WildernessLabs/Netduino_Hardware/N1_Plus/N1Plus_31Aug2010_RevB.pdf

## Power Connector +7.5V to +12V DC Input (9V Preferred)

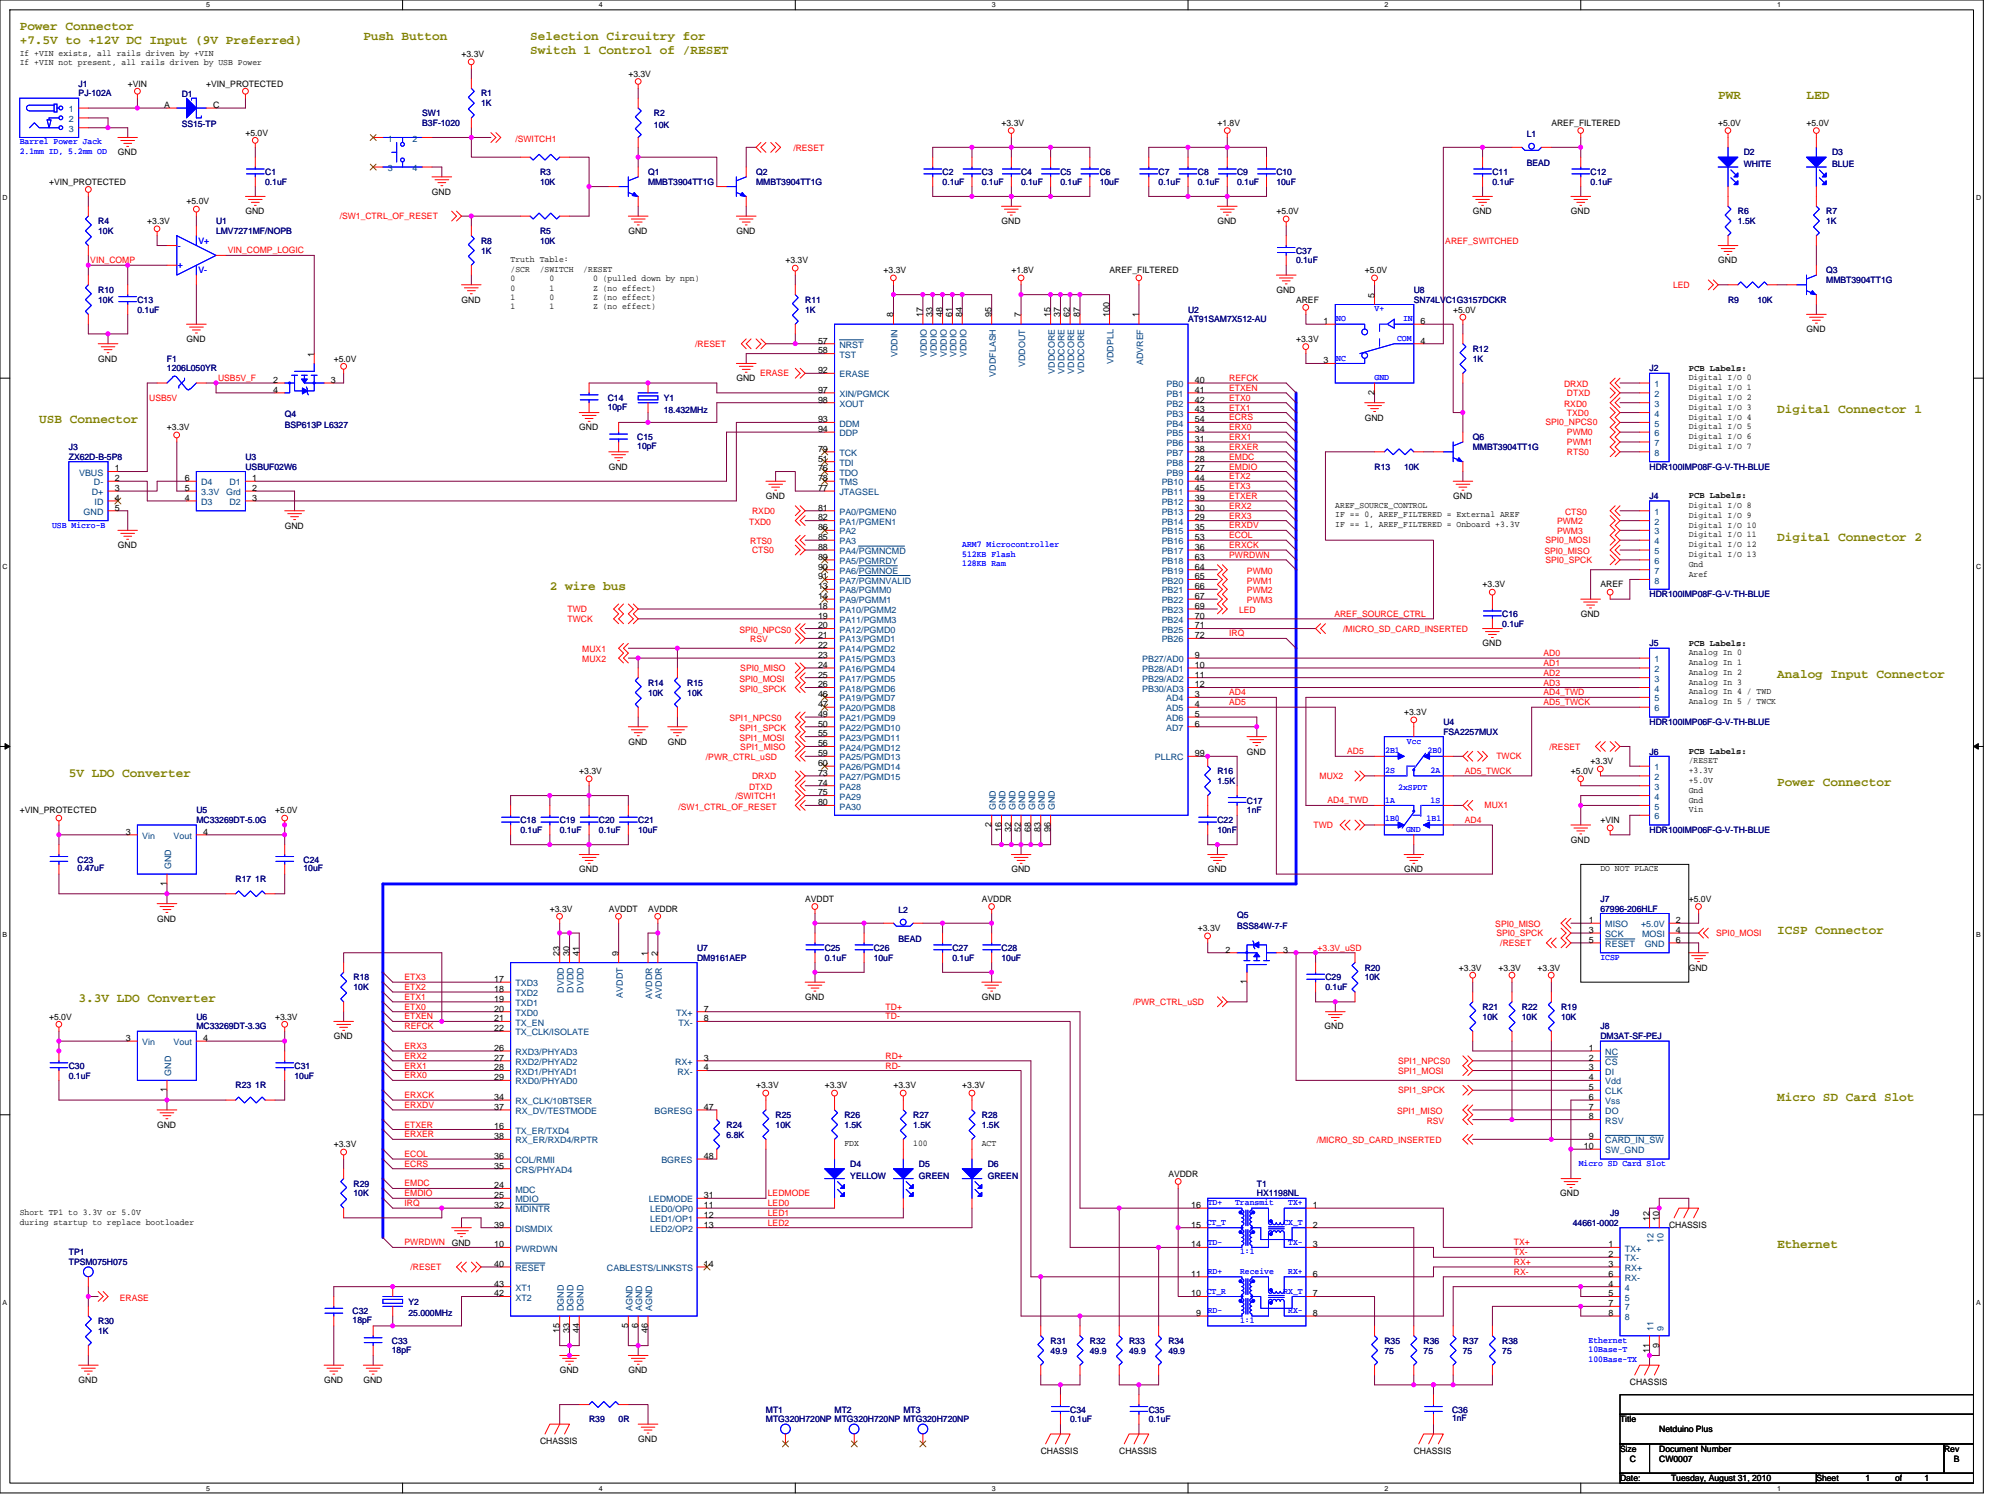
[picture p7: page 1]

Selection Circuitry for
Switch 1 Control of /RESET

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

Micro SD Card Slot

Short TP1 to 3.3V or 5.0V
during startup to replace bootloader
