WildernessLabs/Netduino_Hardware/N2/N2_20Dec16.pdf

## Power Connector

+7V to +9V DC Input | 5V LDO Converter

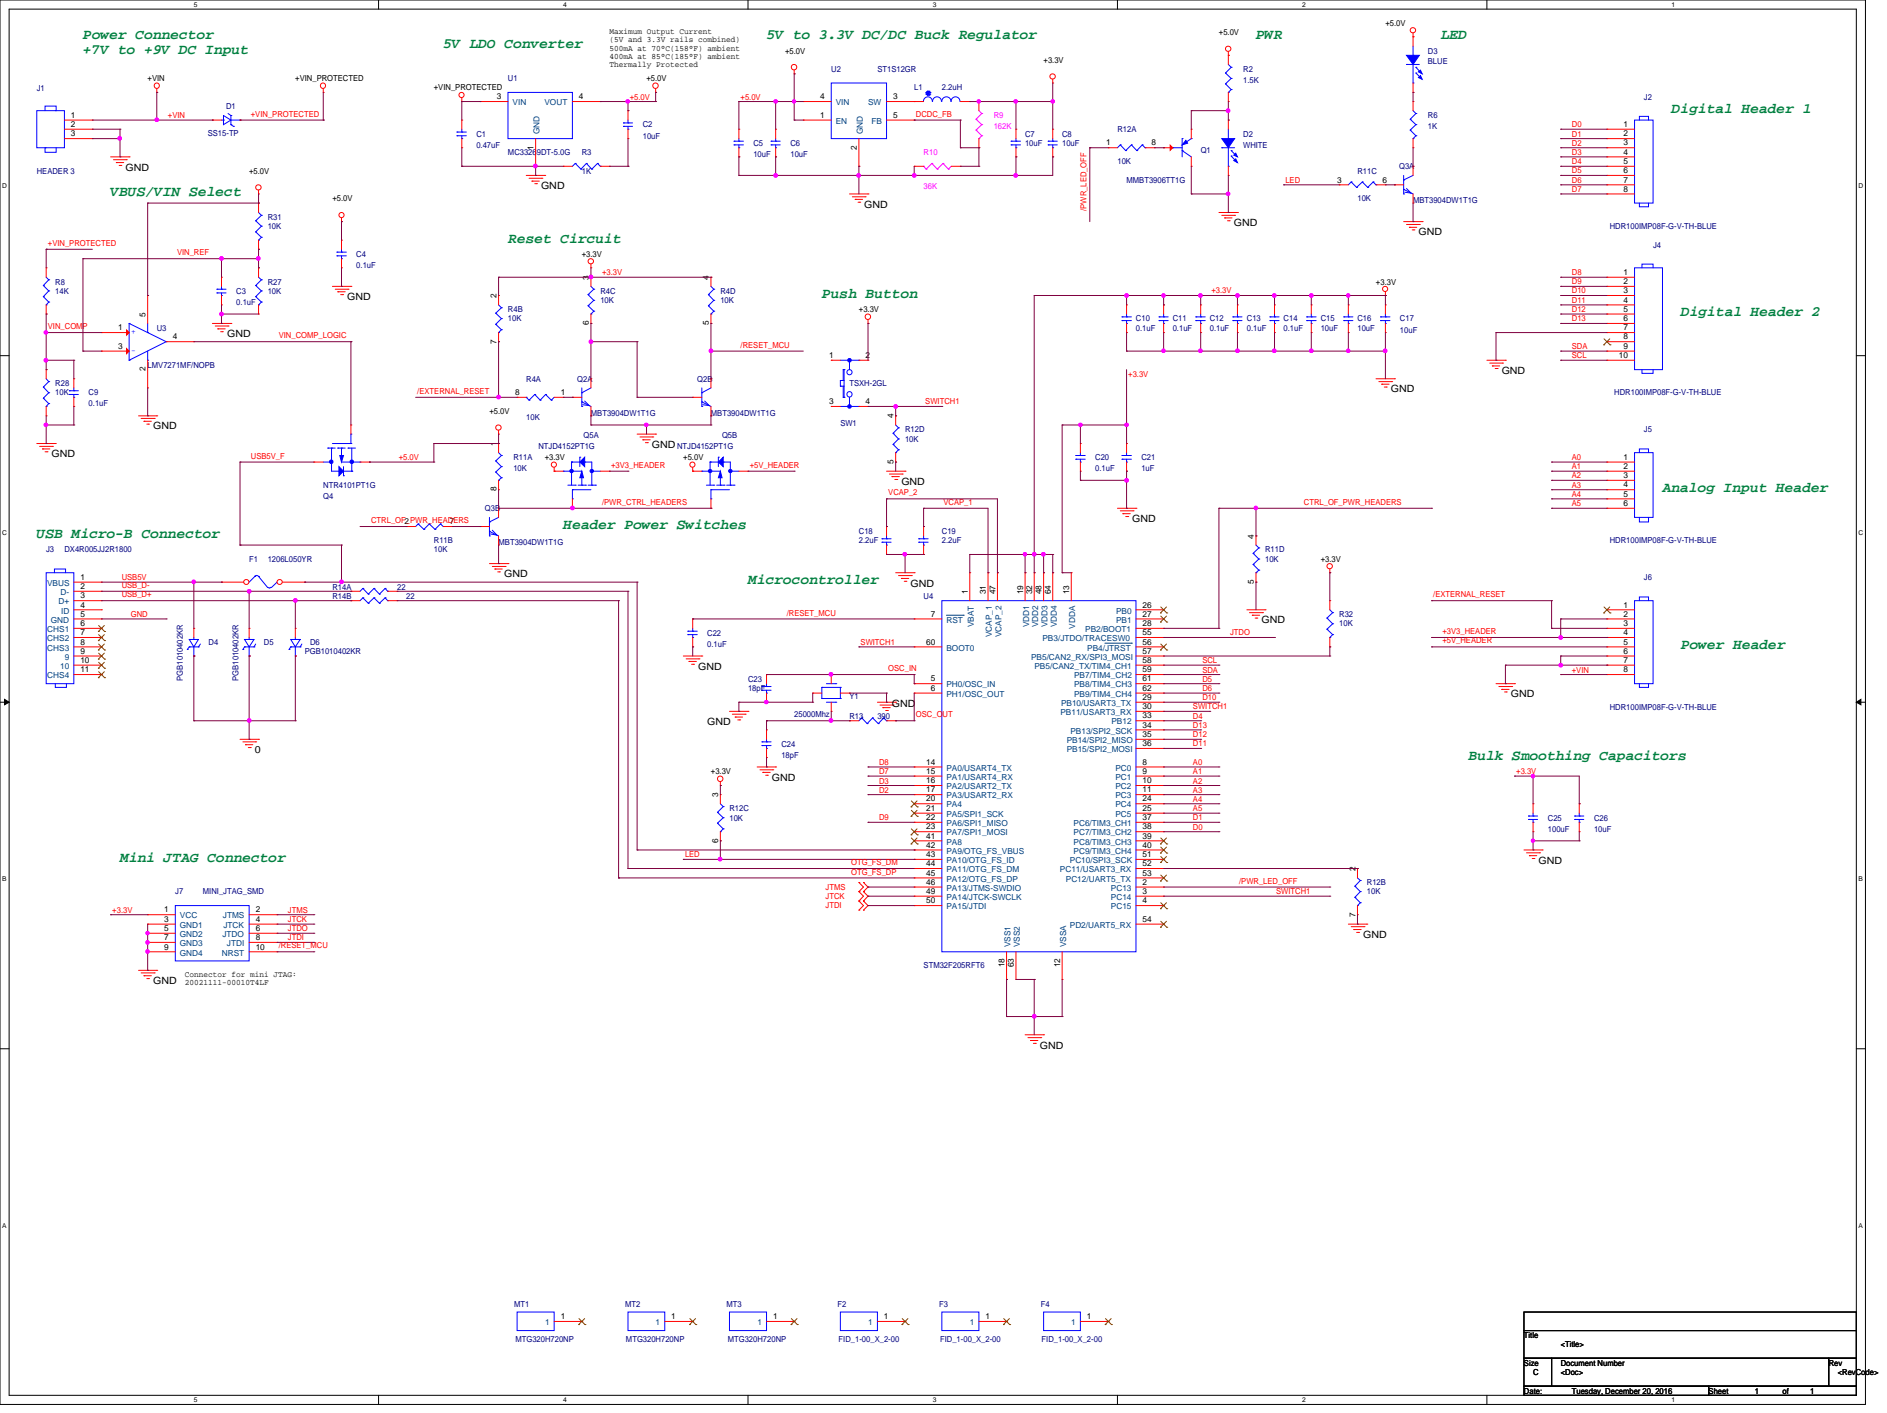
[picture p8: page 1]

5V to 3.3V DC/DC Buck Regulator

41 PA9/OTG_FS_VBUS 42 PA10/OTG_FS_ID 43 PA11/OTG_FS_DM 44 PA12/OTG_FS_DP 45 PA13/JTMS-SWDIO 46 PA14/JTCK-SWCLK 49 PA15/JTDI 50

Connector for mini JTAG:
GND
