WildernessLabs/Netduino_Hardware/N2_Plus/N2_PLUS_20DEC16_0800.pdf

## Power Connector

+7V to +9V DC Input | 5V LDO Converter

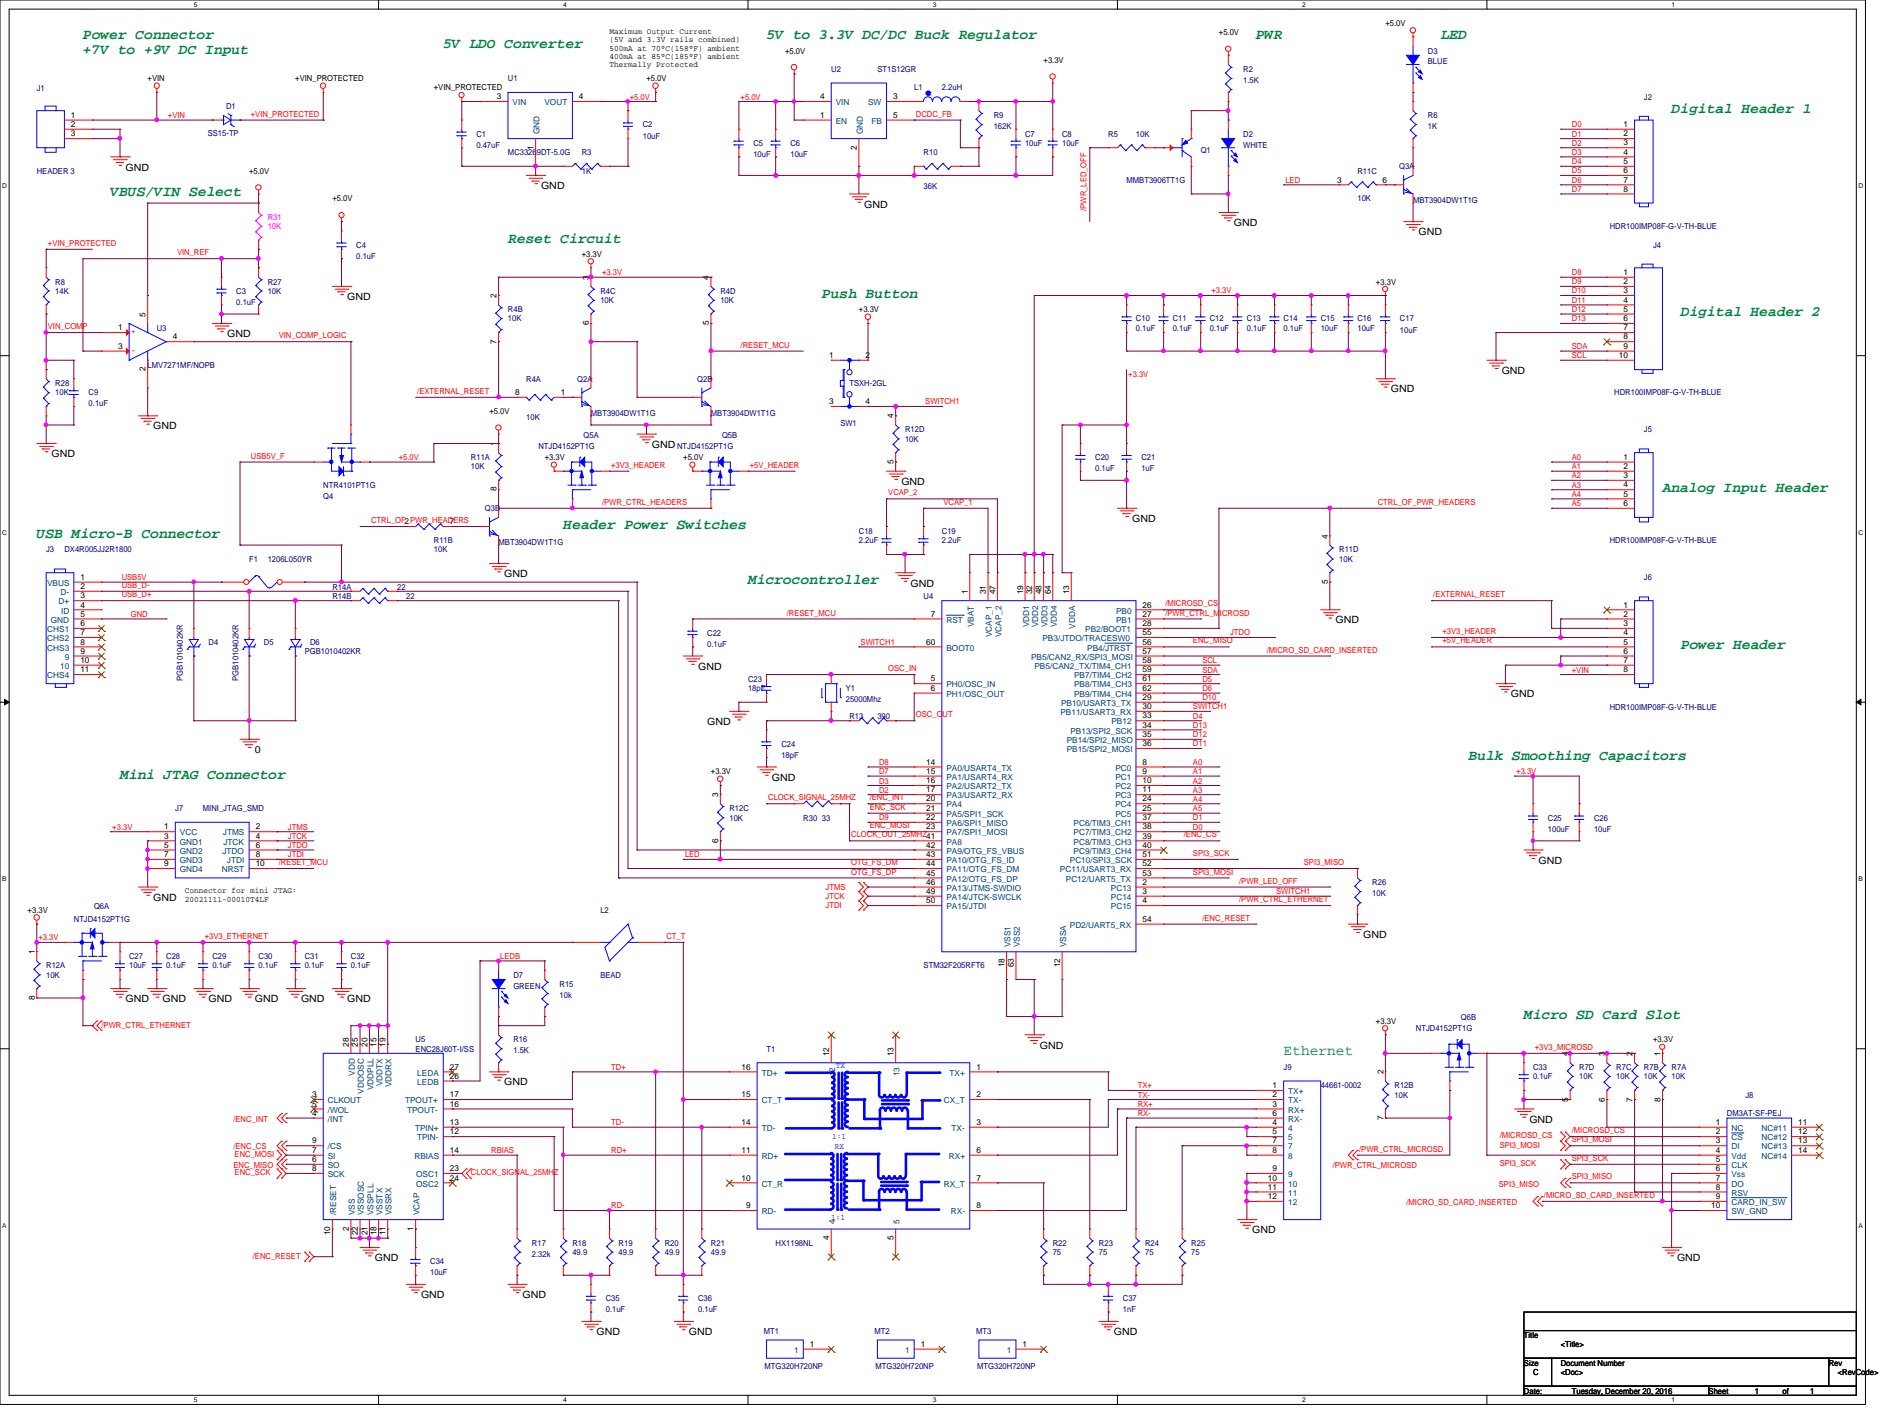
[picture p9: page 1]

5V to 3.3V DC/DC Buck Regulator

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

Connector for mini JTAG:
GND

Micro SD Card Slot

27 VDDRX ¹⁹ VDDTX ¹⁵ VDDPLL 20 VDDOSC ²⁵ VDD ²⁸

J8 DM3AT-SF-PEJ NC 1 CS 2 DI 3 Vdd

4 CLK 5 Vss 6 DO 7 RSV 8 CARD_IN_SW 9 SW_GND 10

2 VSSOSC 22 VSSPLL 21 VSSTX 18 VSSRX 11 VCAP
