WildernessLabs/Netduino_Hardware/N3/NETDUINO3_16DEC16.pdf

## Power Connector

+7V to +12V DC Input | 5V LDO Converter | 5V to 3.3V DC/DC Buck Regulator

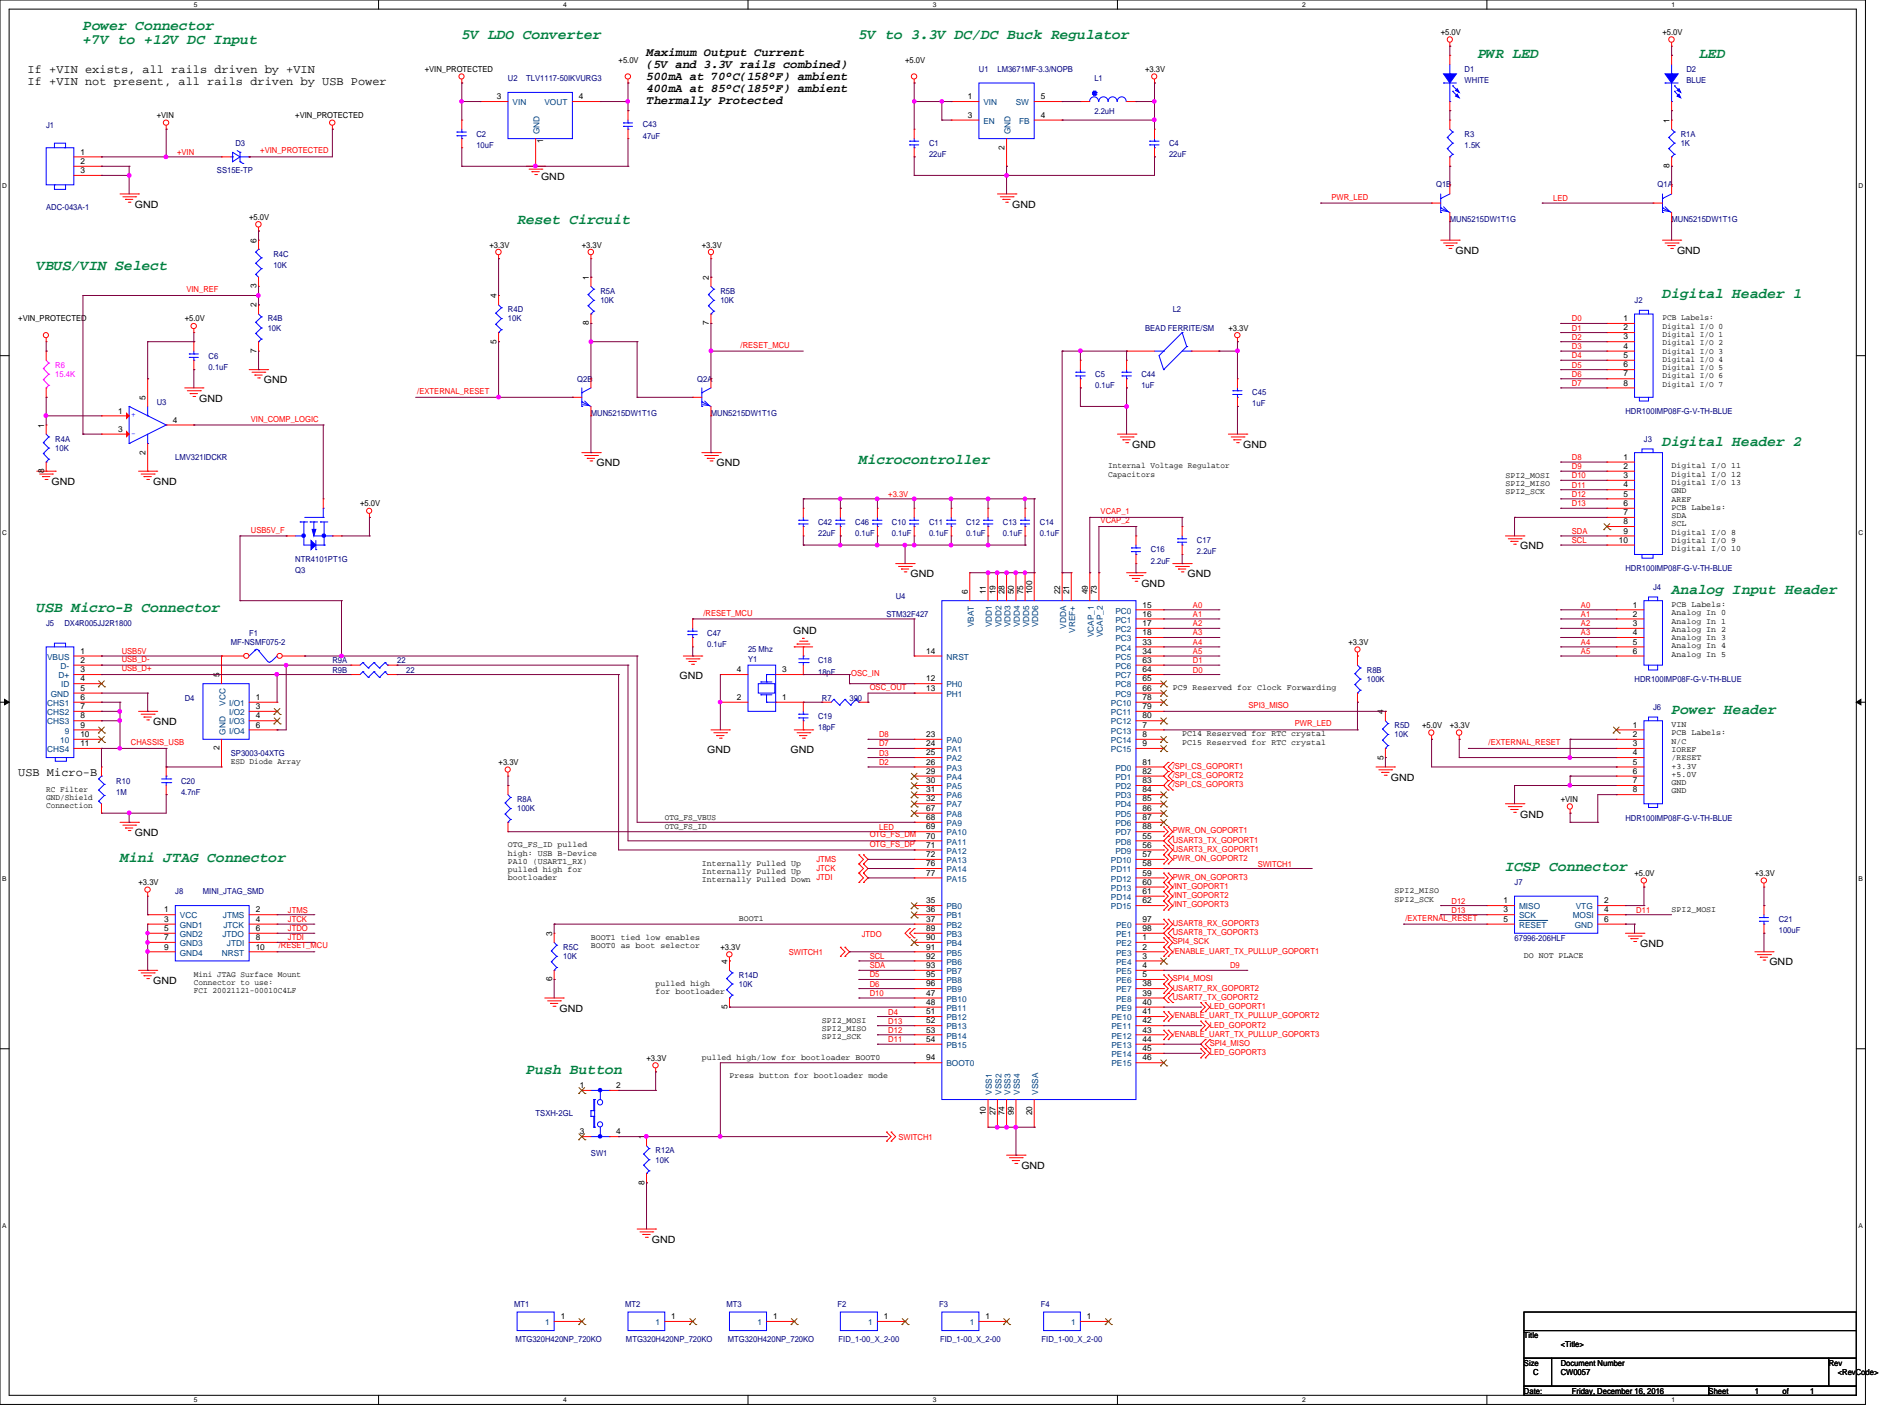
[picture p10: page 1]

If +VIN exists, all rails driven by +VIN
If +VIN not present, all rails driven by USB Power

PC9 Reserved for Clock Forwarding

PC14 Reserved for RTC crystal
PC15 Reserved for RTC crystal

Mini JTAG Surface Mount
Connector to use:
FCI 20021121-00010C4LF

pulled high/low for bootloader BOOT0

Press button for bootloader mode

## GoPort Power Switches

## GoPort1

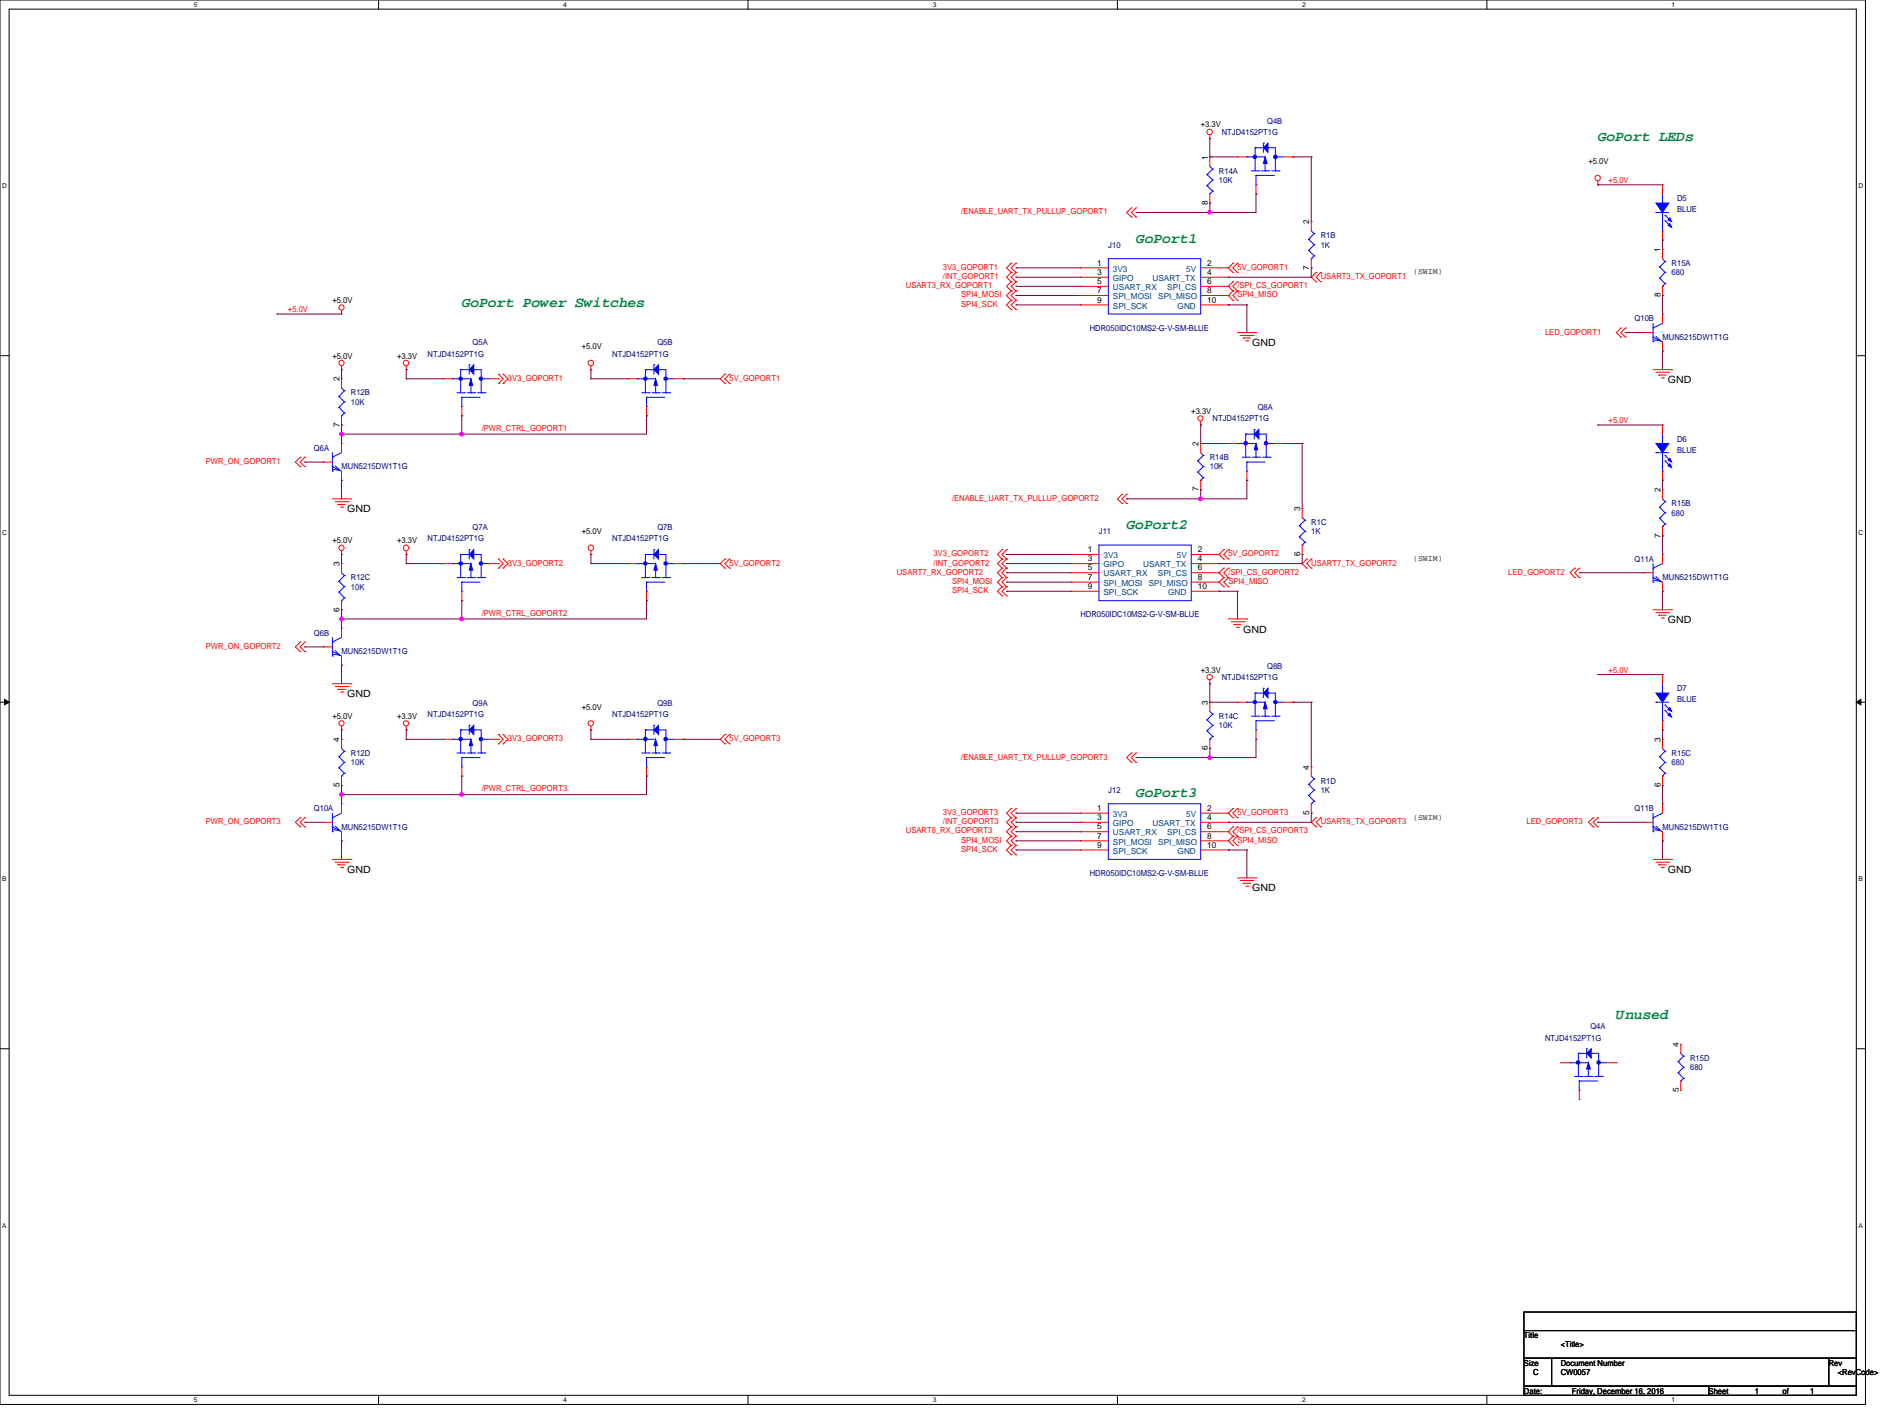
[picture p11: page 2]
