WildernessLabs/Netduino_Hardware/N3_Ethernet/N3_ETHENET_17DEC16_1415.pdf

## Power Connector

+7V to +12V DC Input | 5V LDO Converter | 5V to 3.3V DC/DC Buck Regulator

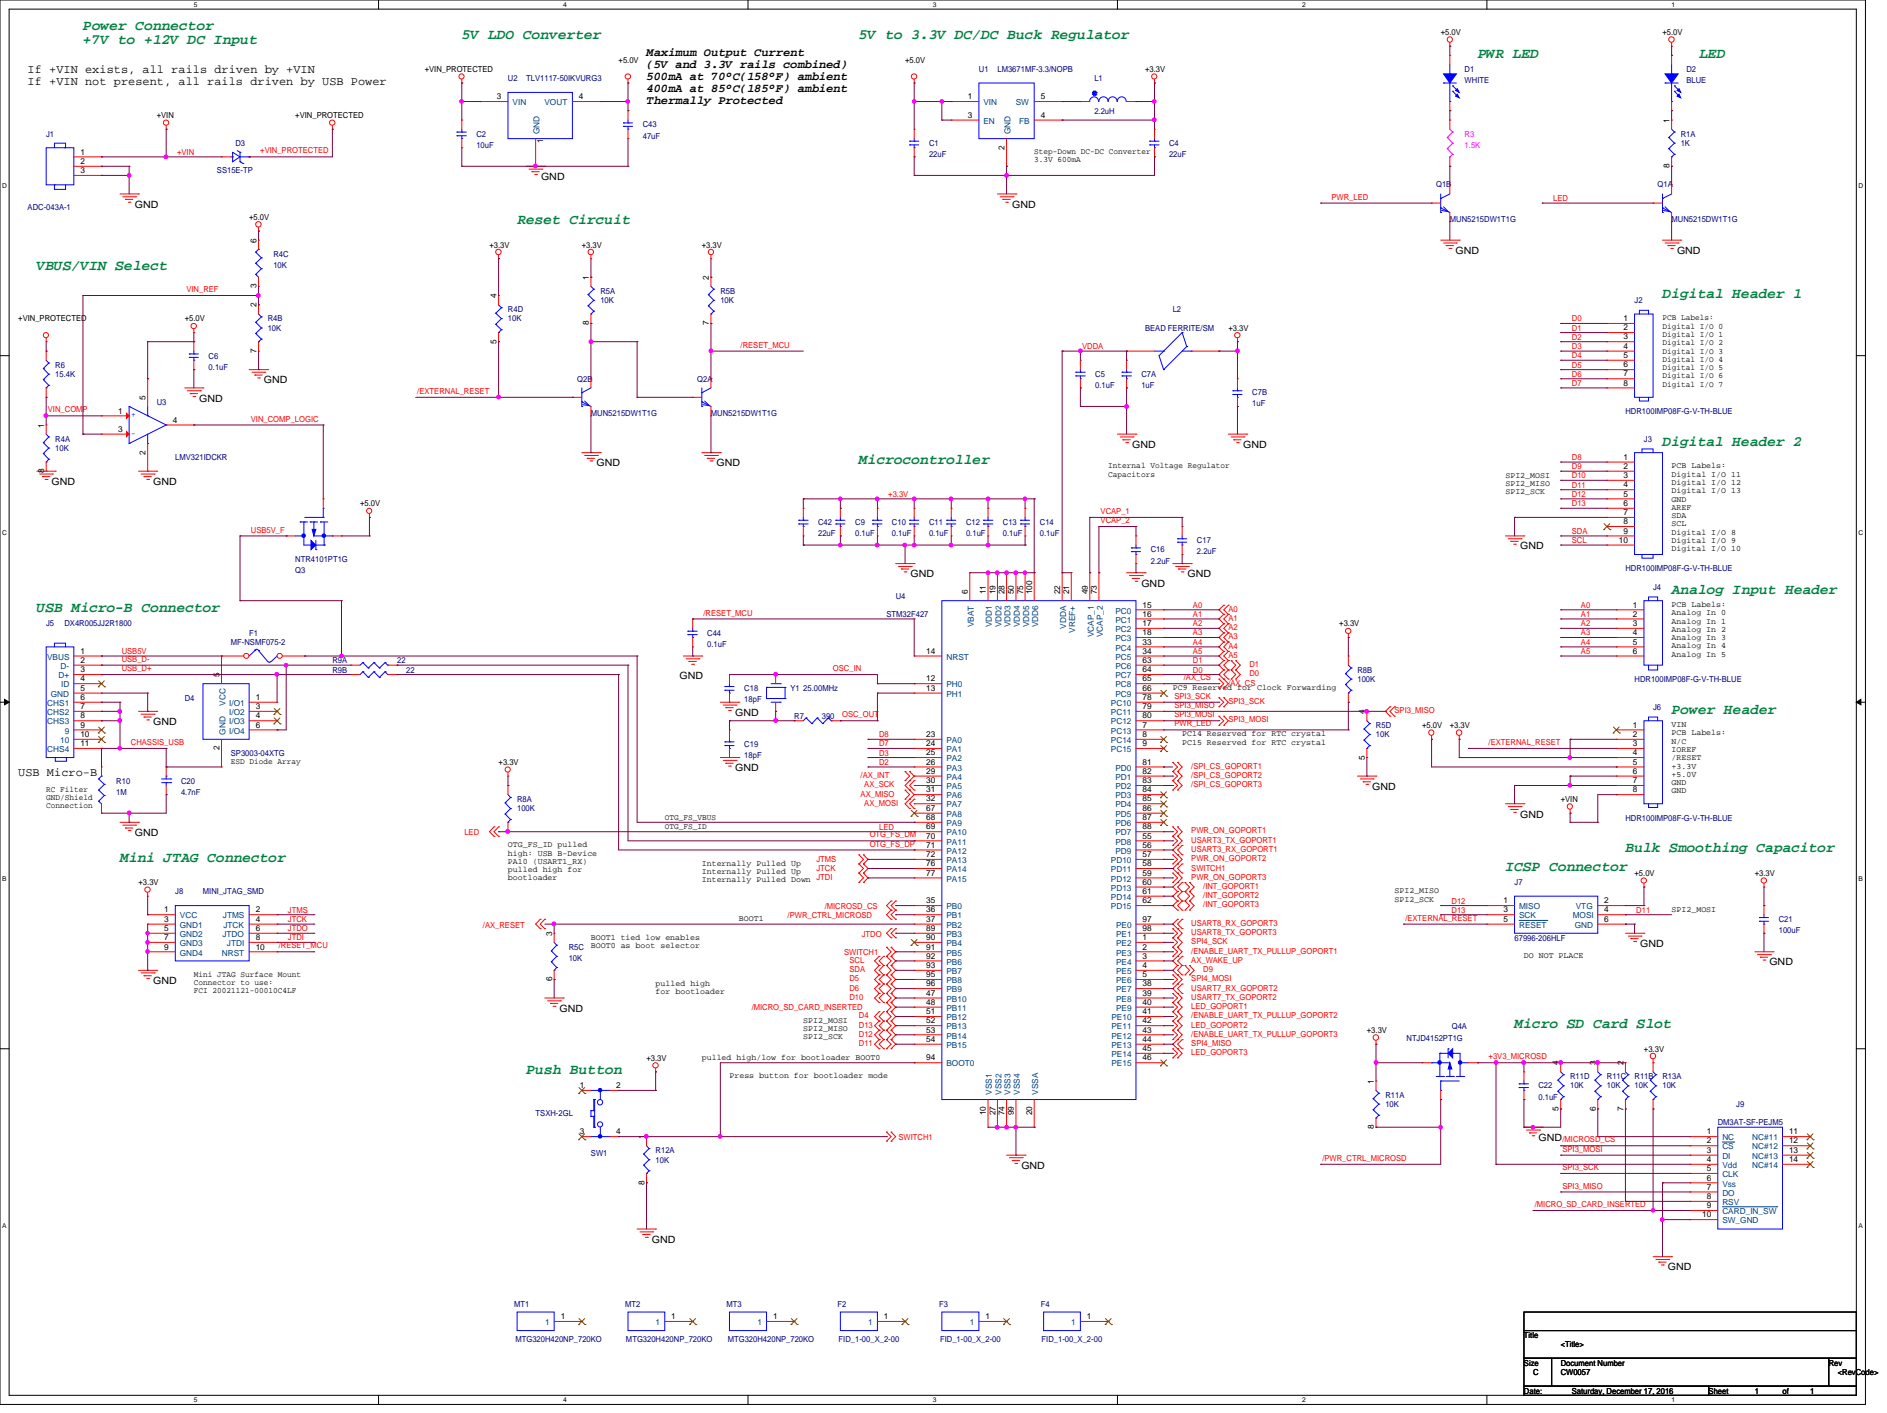
[picture p12: page 1]

If +VIN exists, all rails driven by +VIN
If +VIN not present, all rails driven by USB Power

Step-Down DC-DC Converter

PC14 Reserved for RTC crystal
PC15 Reserved for RTC crystal

Mini JTAG Surface Mount
Connector to use:
FCI 20021121-00010C4LF

Micro SD Card Slot

pulled high/low for bootloader BOOT0

Press button for bootloader mode

J9 DM3AT-SF-PEJM5 NC 1 CS 2 DI 3 Vdd

4 CLK 5 Vss 6 DO 7 RSV 8 CARD_IN_SW 9 SW_GND 10

## GoPort Power Switches

## GoPort1

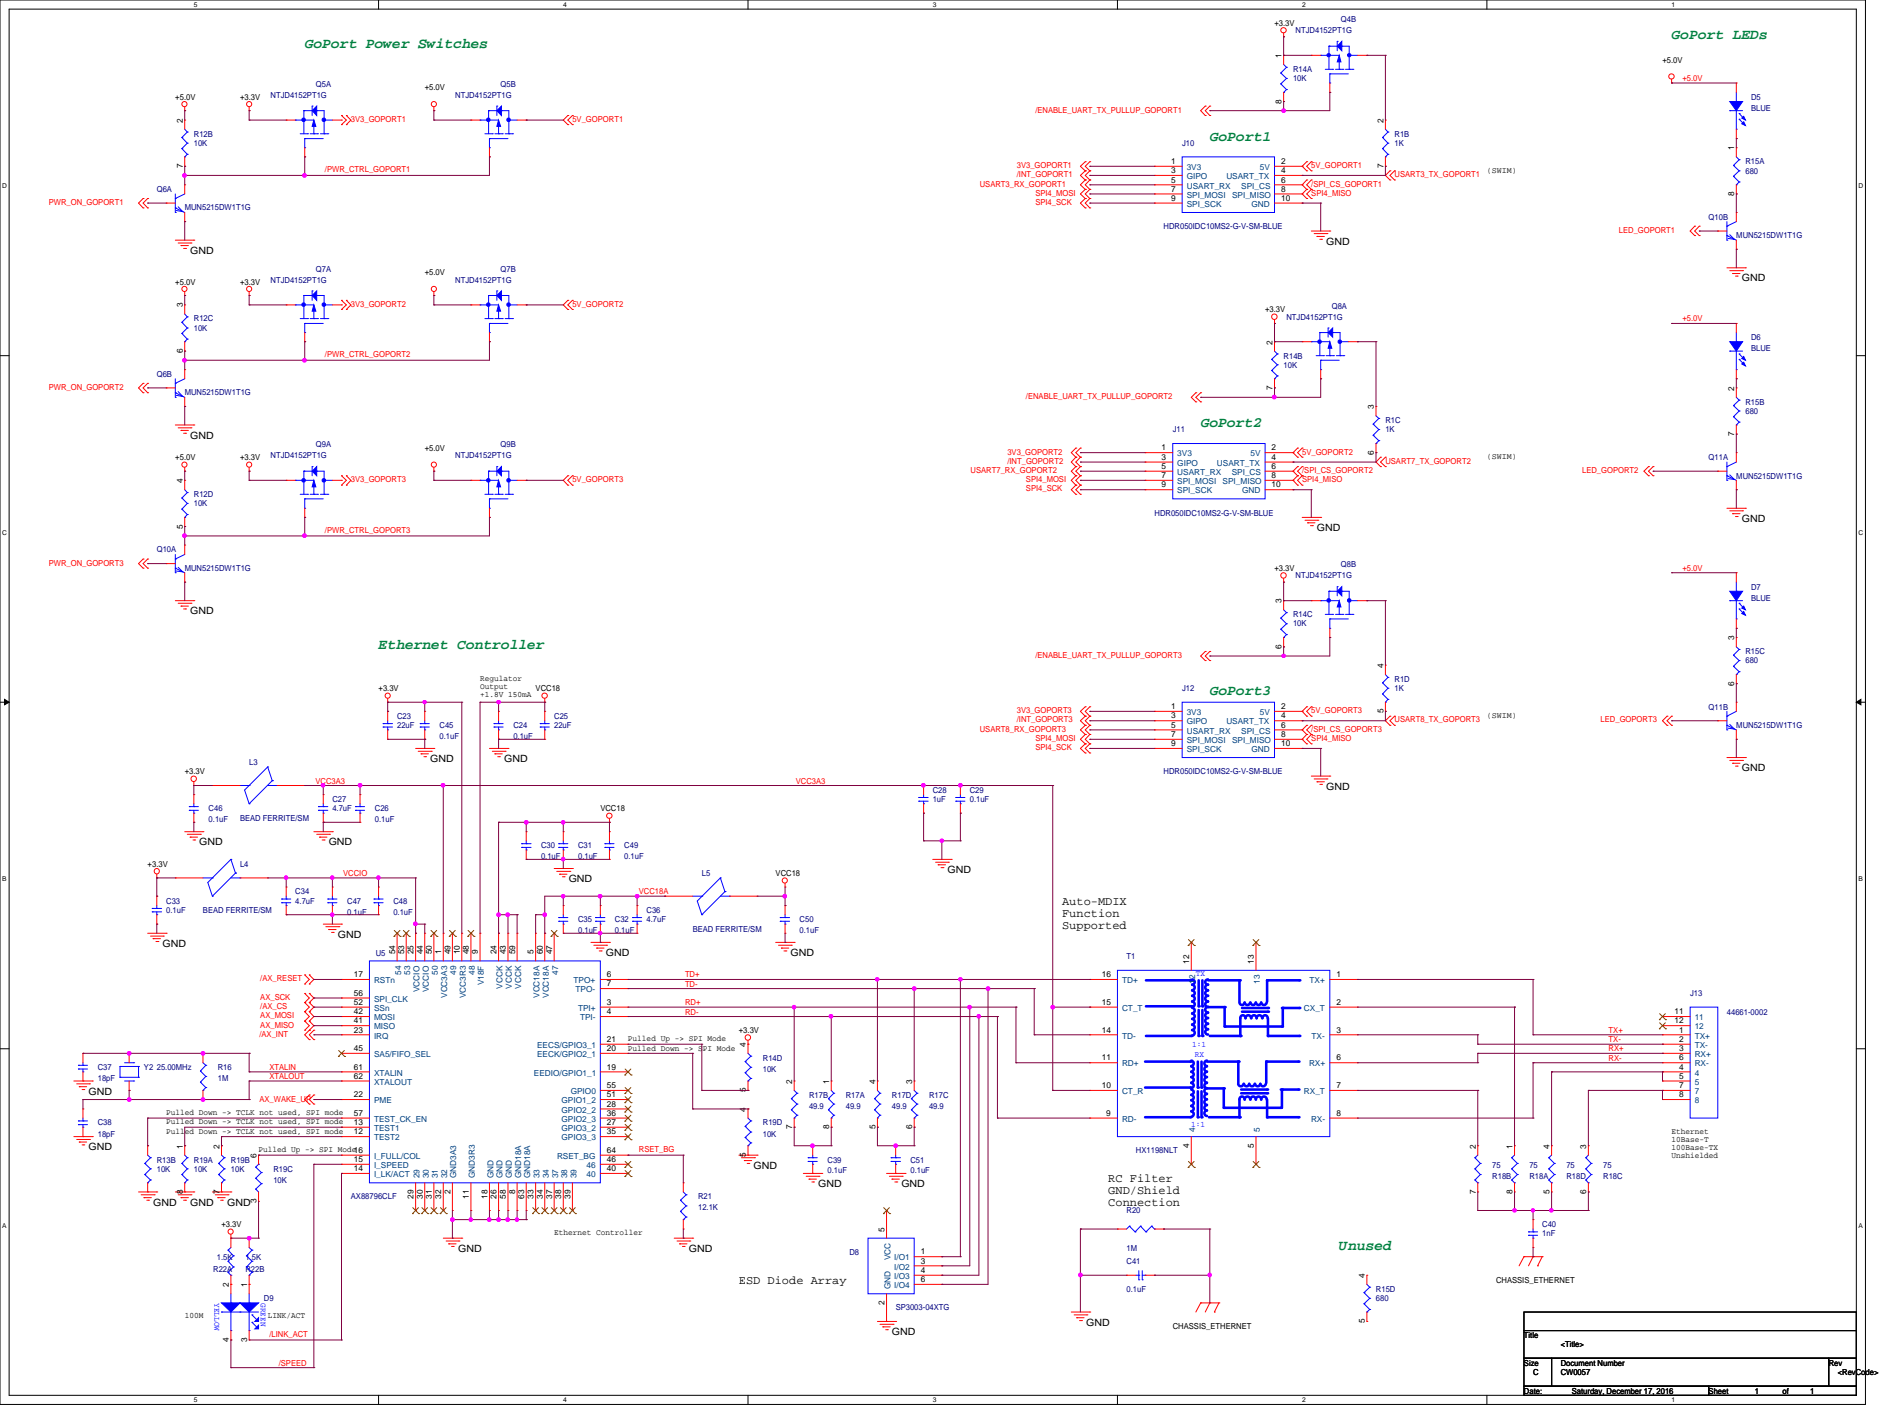
[picture p13: page 2]

TPO+ 6 TPO- 7 VCC¹⁸A ⁶⁰ VCC¹⁸A

RSTn 17 SPI_CLK 56 SSn 52 MOSI 42 MISO 41

Pulled Up -> SPI Mode
Pulled Down -> SPI Mode

Pulled Down -> TCLK not used, SPI mode
