WildernessLabs/Netduino_Hardware/N3_WiFi/N3_WIFI_13DEC16_0800.pdf

## Power Connector +7V to +12V DC Input

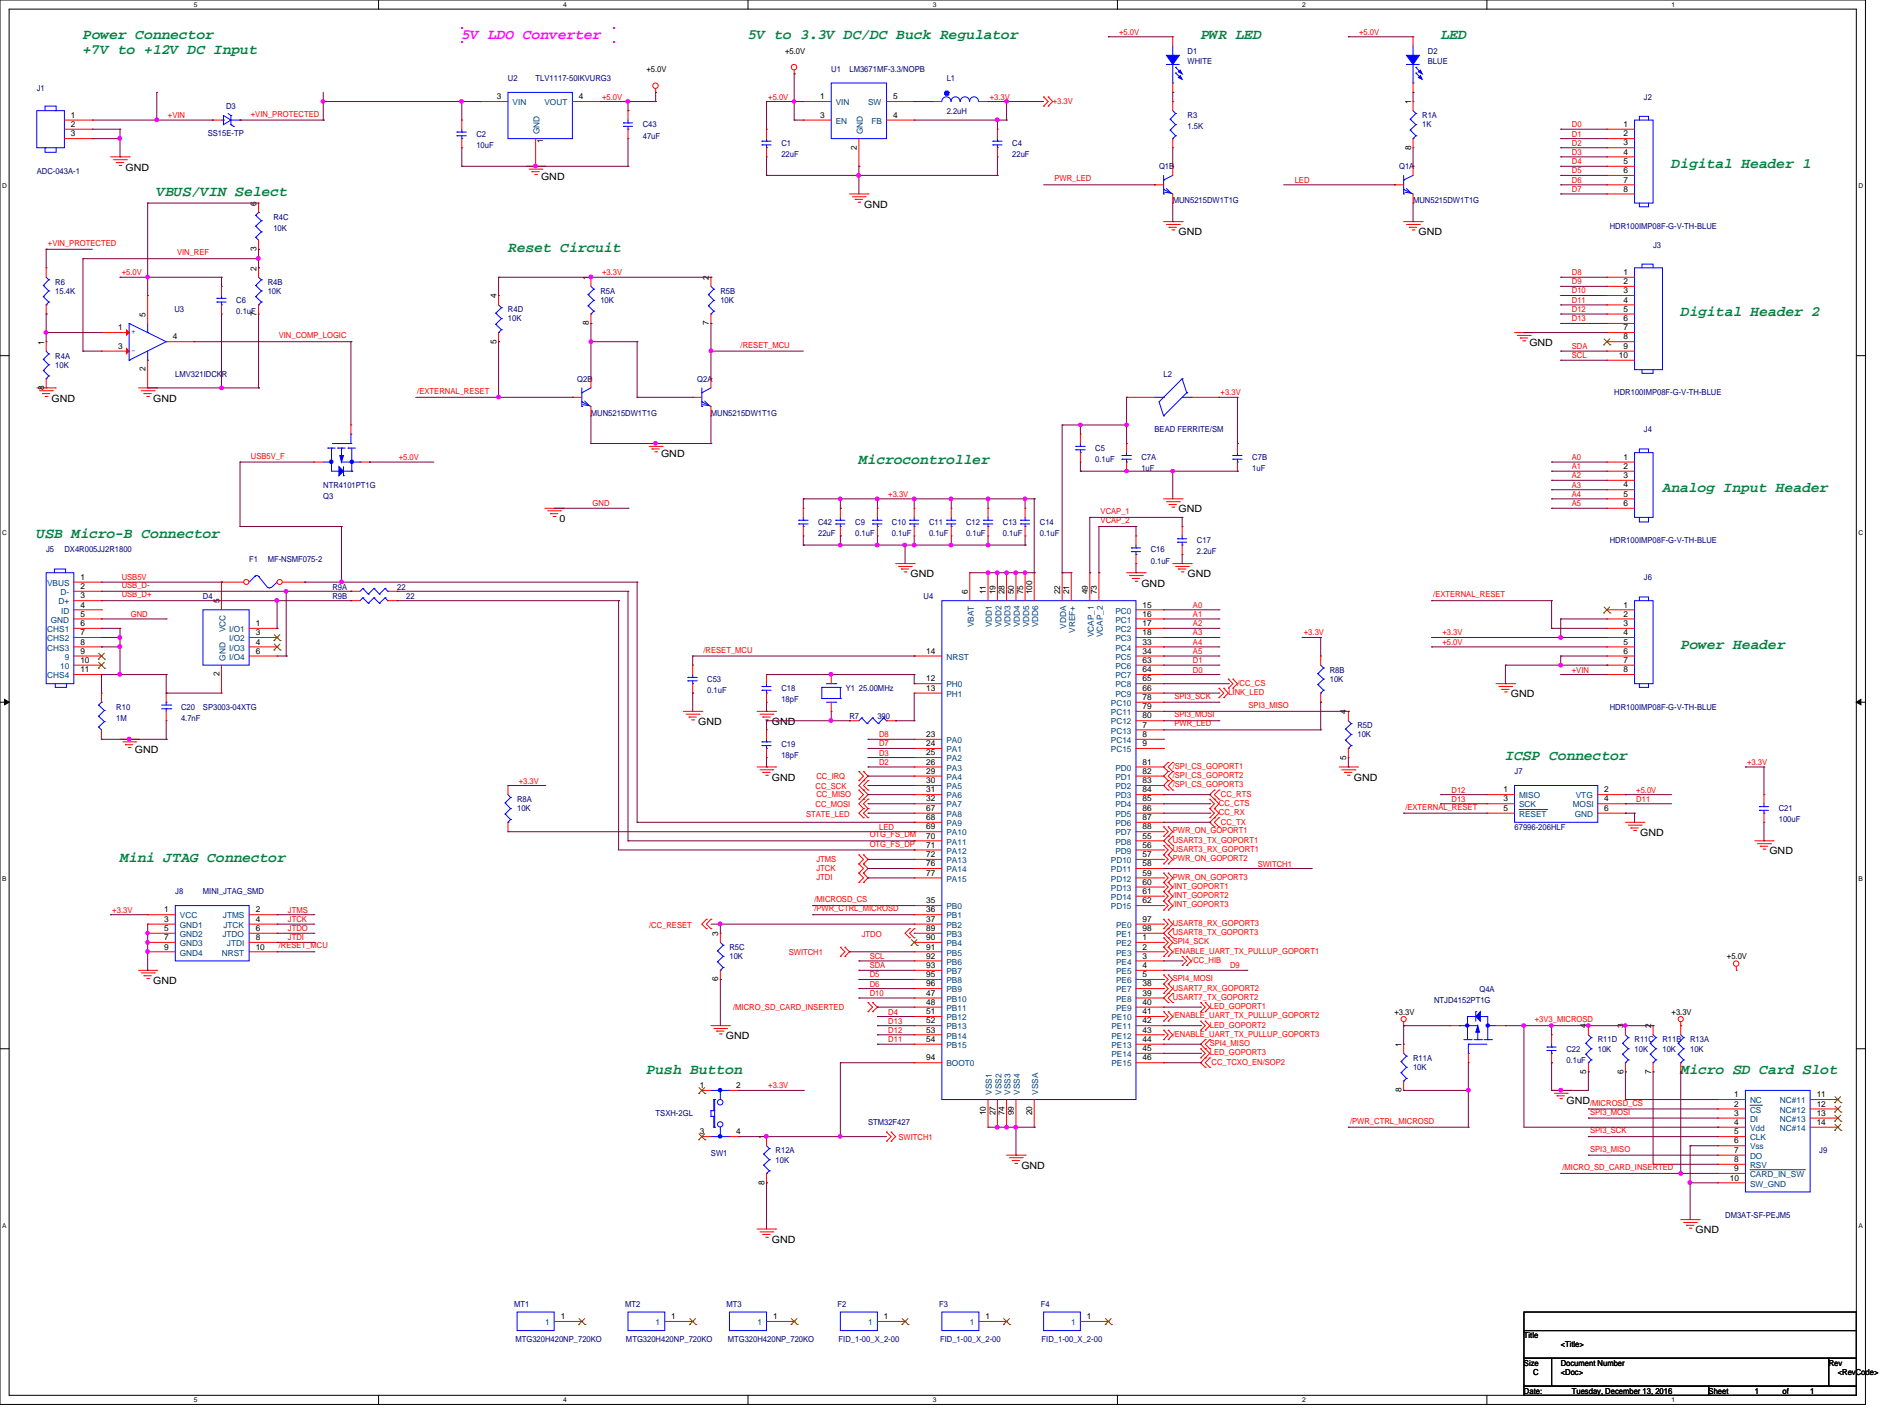
[picture p14: page 1]

NC 1 CS 2 DI 3 Vdd

4 CLK 5 Vss 6 DO 7 RSV 8 CARD_IN_SW 9 SW_GND 10

## GoPort Power Switches

## GoPort1

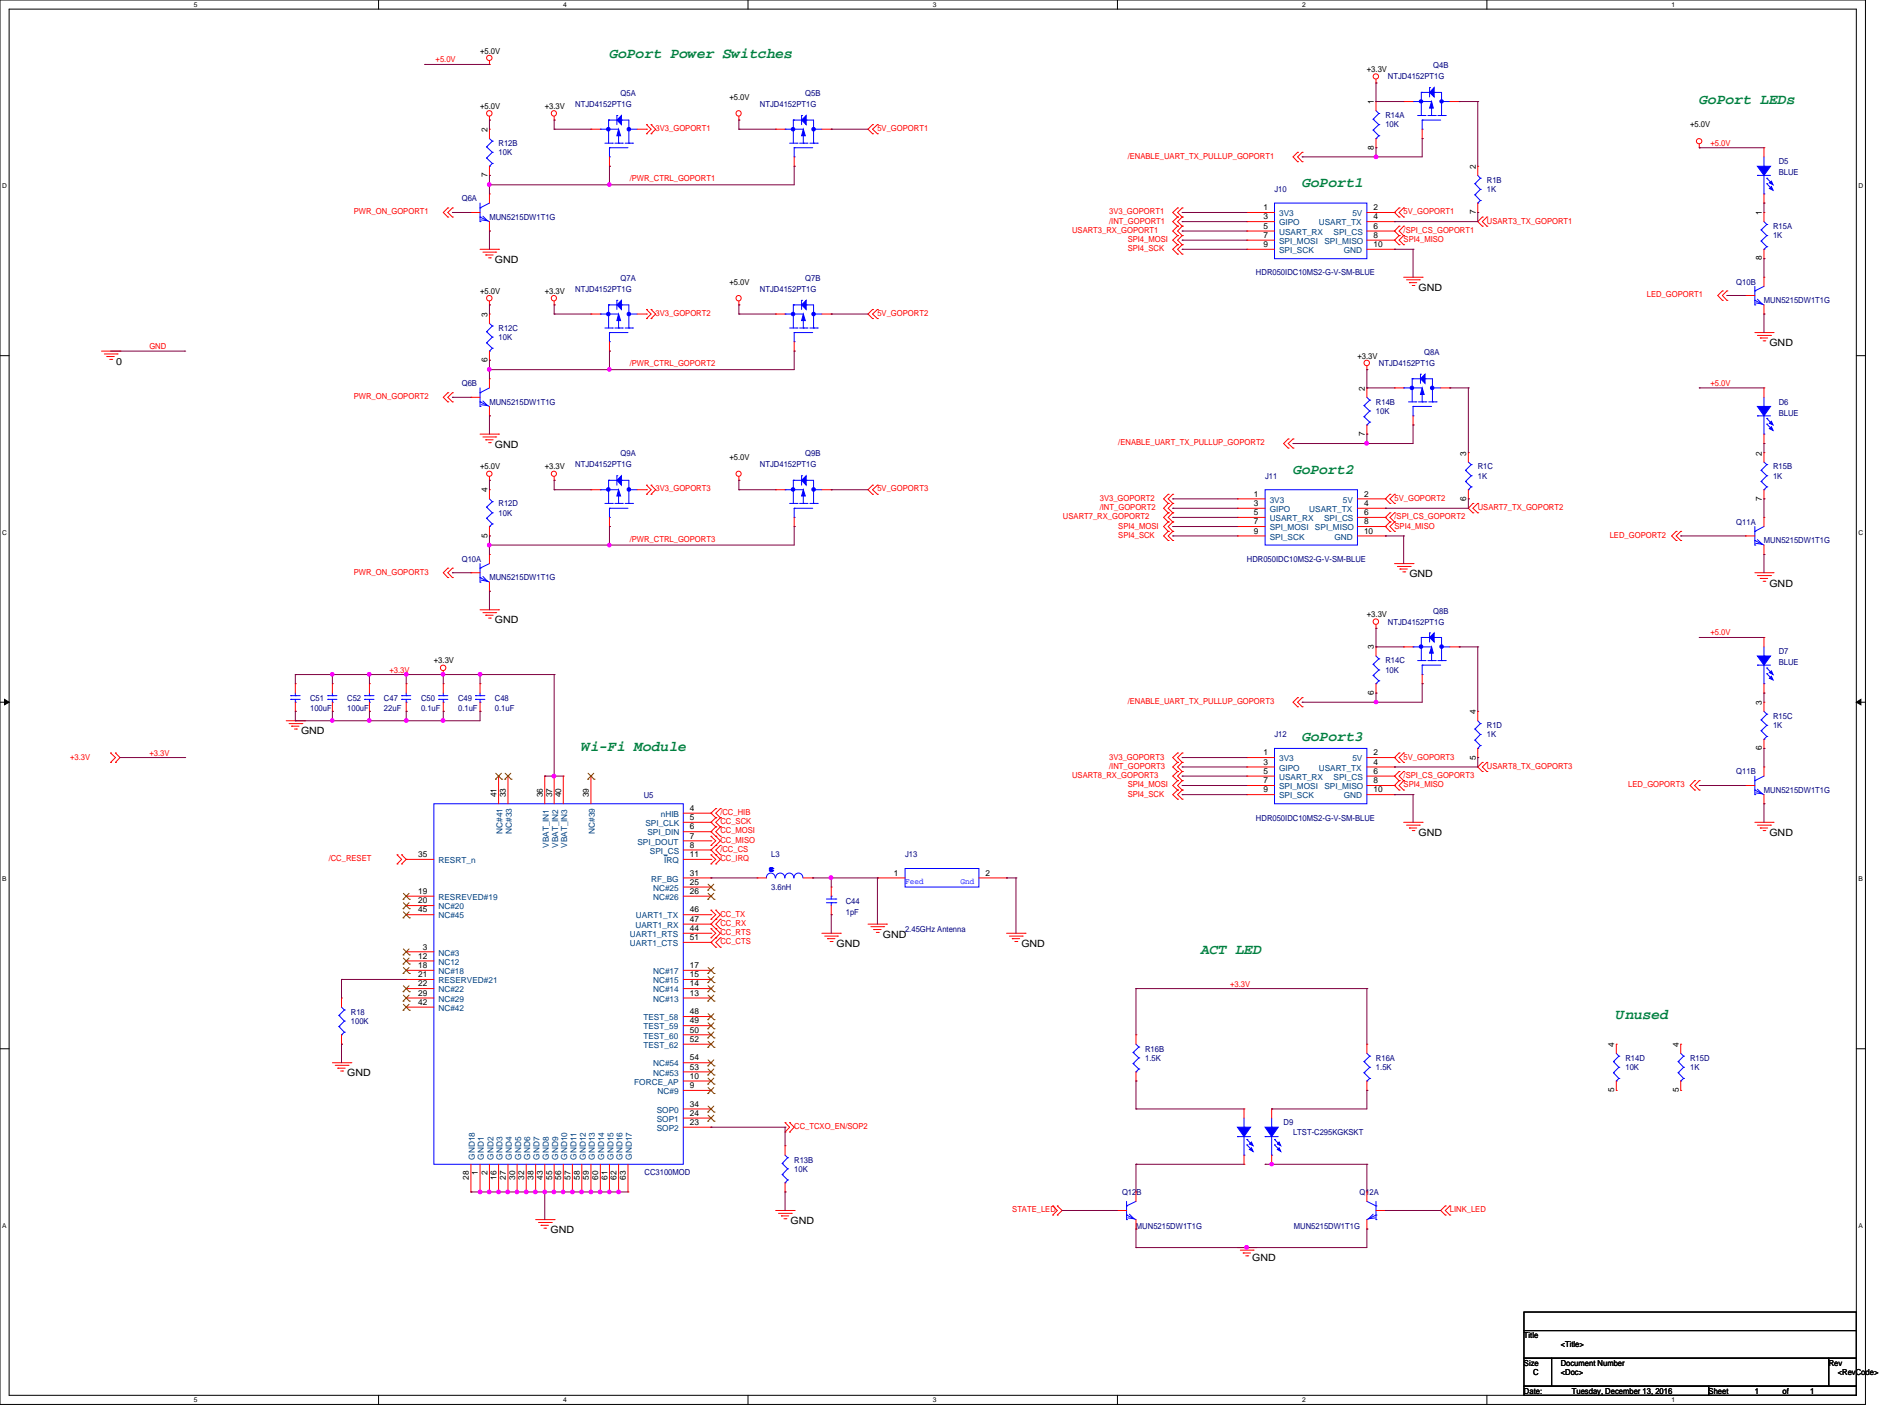
[picture p15: page 2]

NC#3 3 NC12 12 NC#18 18 RESERVED#21 21 NC#22 22 NC#29 29 NC#42 42

NC#17 17 NC#15 15 NC#14 14 NC#13 13 TEST_58 48 TEST_59 49 TEST_60 50 TEST_62 52 NC#53 53 NC#54 54 NC#9 9 FORCE_AP 10 SOP0 34 SOP1 24 SOP2 23 GND¹
