WildernessLabs/Netduino_Hardware/N3/Netduino3_16Dec16_0800_FAB/Netduino3_16Dec16_0800_NC_DRL_1-4.pdf

## ART FILM - NC_DRL_1-4

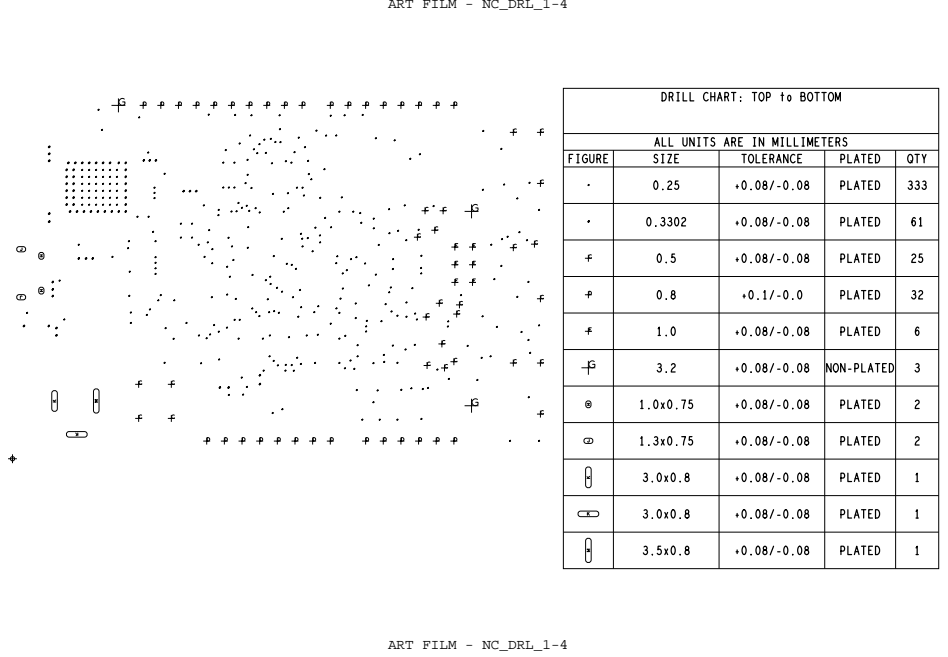
[picture p18: page 1]
ART FILM - NC_DRL_1-4

DRILL CHART: TOP to BOTTOM

ALL UNITS ARE IN MILLIMETERS

FIGURE | SIZE | TOLERANCE | PLATED | QTY

0.25 | +0.08/-0.08 | PLATED | 333

0.3302 | +0.08/-0.08 | PLATED | 61

0.5 | +0.08/-0.08 | PLATED | 25

0.8 | +0.1/-0.0 | PLATED | 32

1.0 | +0.08/-0.08 | PLATED | 6

3.2 | +0.08/-0.08 | NON-PLATED | 3

1.0x0.75 | +0.08/-0.08 | PLATED | 2

1.3x0.75 | +0.08/-0.08 | PLATED | 2

3.0x0.8 | +0.08/-0.08 | PLATED | 1

3.5x0.8 | +0.08/-0.08 | PLATED | 1
