WildernessLabs/Netduino_Hardware/N3_Ethernet/Netduino3Ethernet_17Dec16_FAB/Netduino3Ethernet_17Dec16_NC_DRL_1-4.pdf

## ART FILM - NC_DRL_1-4

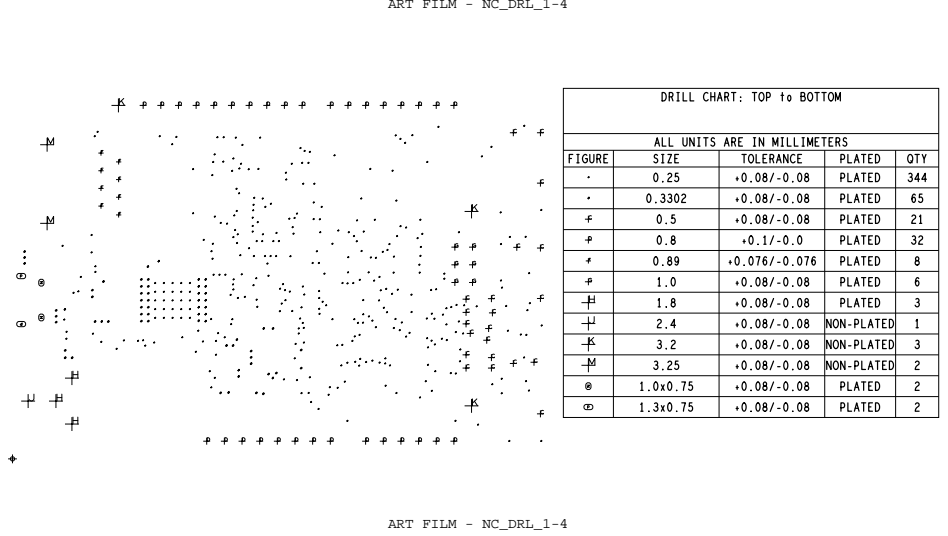
[picture p19: page 1]
ART FILM - NC_DRL_1-4

DRILL CHART: TOP to BOTTOM

ALL UNITS ARE IN MILLIMETERS

FIGURE | SIZE | TOLERANCE | PLATED | QTY

0.25 | +0.08/-0.08 | PLATED | 344
0.3302 | +0.08/-0.08 | PLATED | 65
0.5 | +0.08/-0.08 | PLATED | 21
0.8 | +0.1/-0.0 | PLATED | 32
0.89 | +0.076/-0.076 | PLATED | 8
1.0 | +0.08/-0.08 | PLATED | 6
1.8 | +0.08/-0.08 | PLATED | 3
2.4 | +0.08/-0.08 | NON-PLATED | 1
3.2 | +0.08/-0.08 | NON-PLATED | 3
3.25 | +0.08/-0.08 | NON-PLATED | 2
1.0x0.75 | +0.08/-0.08 | PLATED | 2
1.3x0.75 | +0.08/-0.08 | PLATED | 2
